CedarGroveStudios/PCB_Ibanez_FL-9_Flanger/media/2022-11-17_pcb_before.jpeg

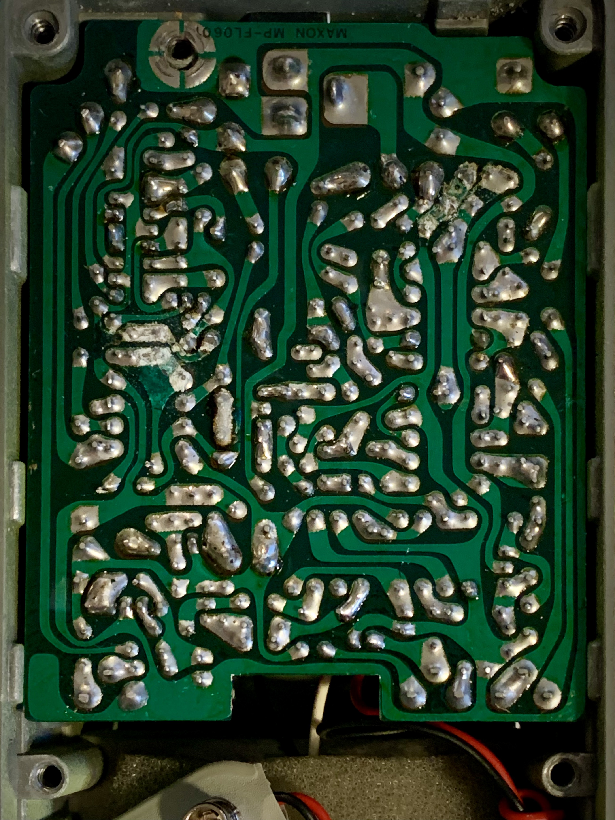
media/2022-11-17_pcb_before.jpeg
