CedarGroveStudios/PCB_Ibanez_FL-9_Flanger/media/cache_31260282.jpg

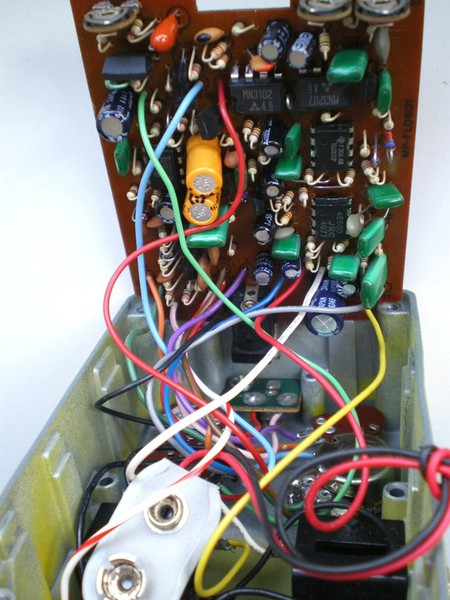
media/cache_31260282.jpg
