CedarGroveStudios/PCB_Ibanez_FL-9_Flanger/media/DigiKey_shipment_2022-11-08.jpeg

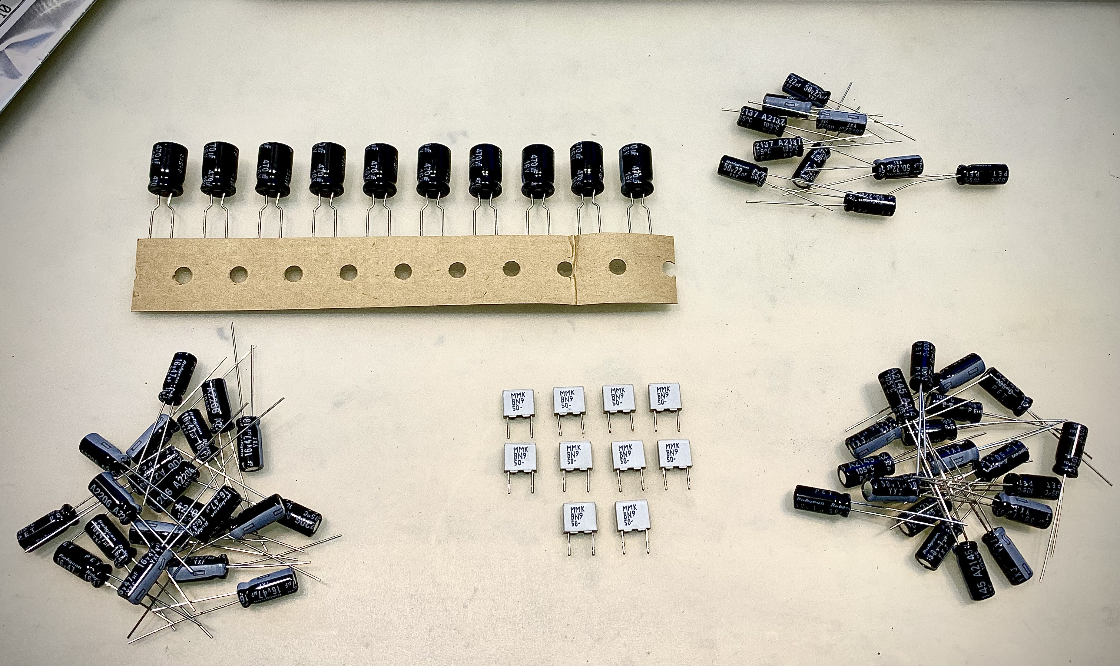
media/DigiKey_shipment_2022-11-08.jpeg
