CedarGroveStudios/PCB_Ibanez_FL-9_Flanger/media/FL9_cap-damaged-in-progress_2022-11-18.jpeg

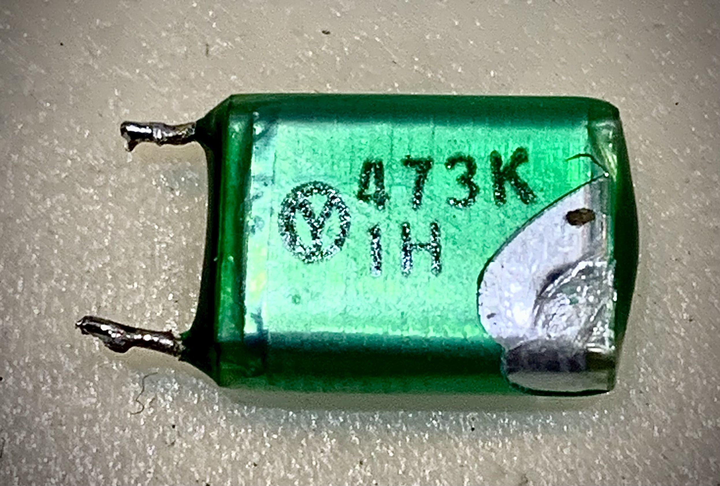
media/FL9_cap-damaged-in-progress_2022-11-18.jpeg
