CedarGroveStudios/PCB_Ibanez_FL-9_Flanger/media/FL9_PCB_before_close02_2022-11-17.jpeg

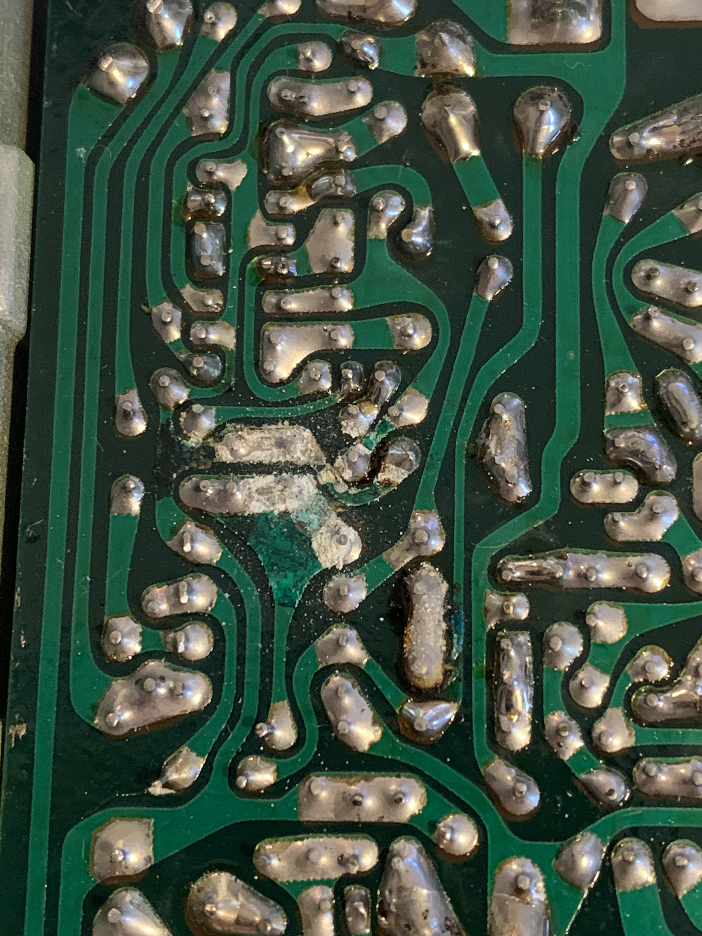
media/FL9_PCB_before_close02_2022-11-17.jpeg
