CedarGroveStudios/PCB_Ibanez_FL-9_Flanger/media/PCB_cleaned_before_close_02_2022-11-17.jpeg

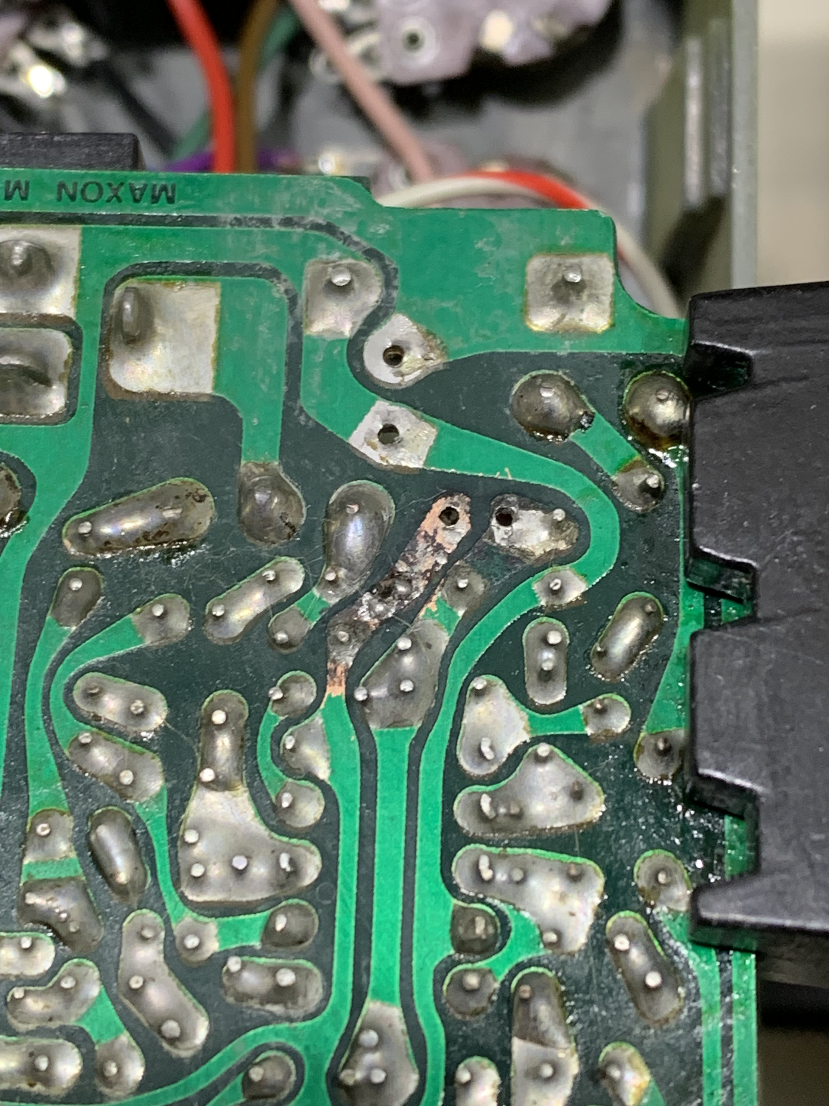
media/PCB_cleaned_before_close_02_2022-11-17.jpeg
