CedarGroveStudios/PCB_Ibanez_FL-9_Flanger/media/PCB_in-progress_close_03_2022-11-17.WEBP

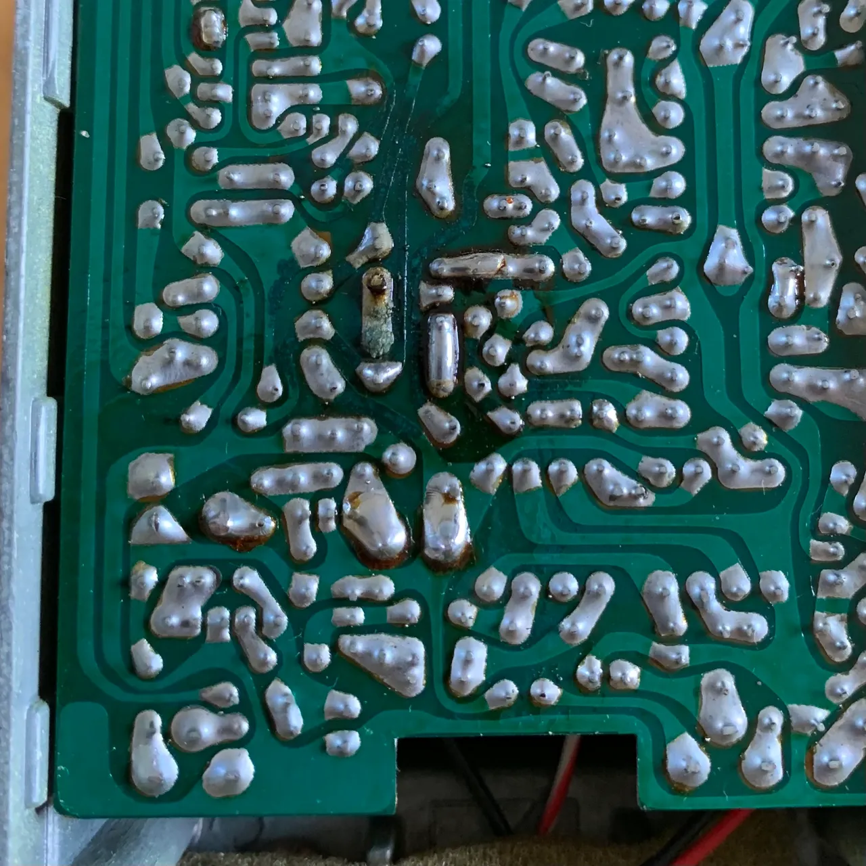
media/PCB_in-progress_close_03_2022-11-17.WEBP
