CedarGroveStudios/PCB_Ibanez_FL-9_Flanger/media/PCB_in-progress_close_04_2022-11-17.jpeg

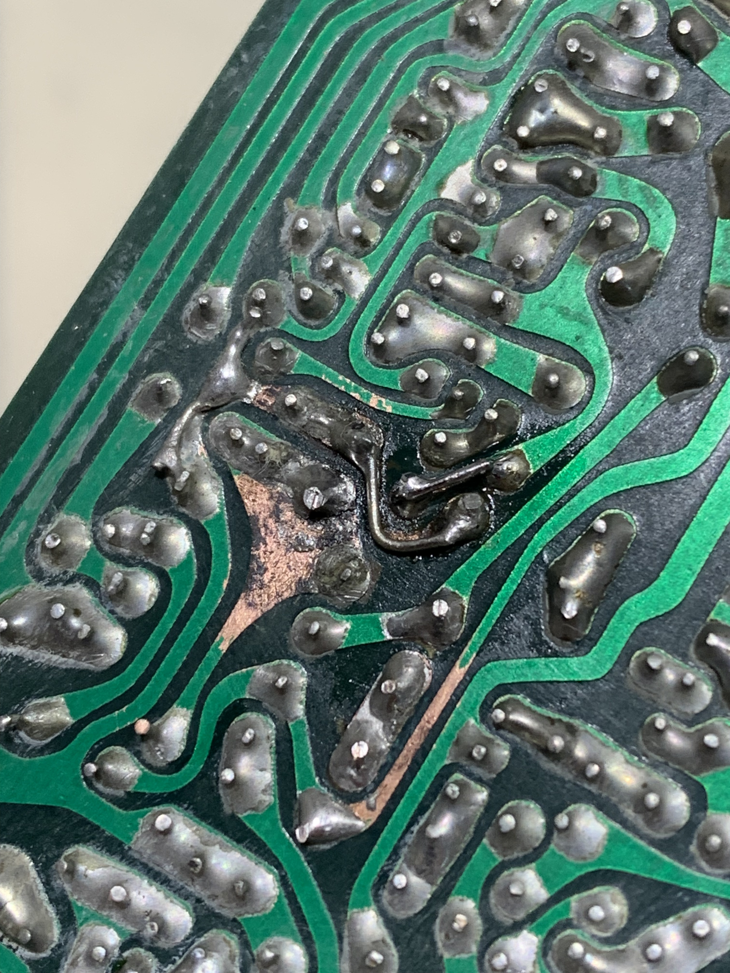
media/PCB_in-progress_close_04_2022-11-17.jpeg
