CedarGroveStudios/PCB_Ibanez_FL-9_Flanger/media/PCB_TOP_before_2022-11-17.jpeg

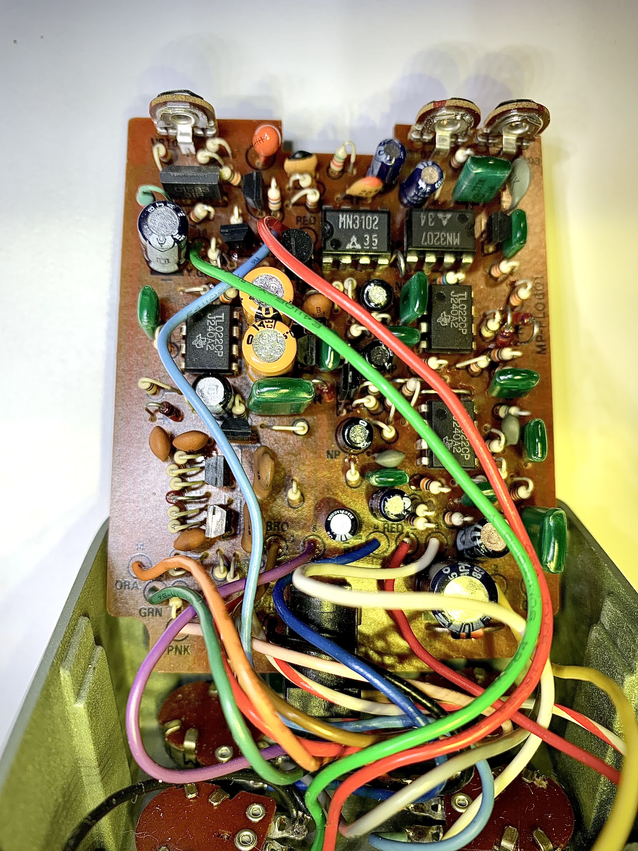
media/PCB_TOP_before_2022-11-17.jpeg
