CedarGroveStudios/PCB_Ibanez_FL-9_Flanger/PCB/FL9_PCB_BOT_traces_60x77mm.jpg

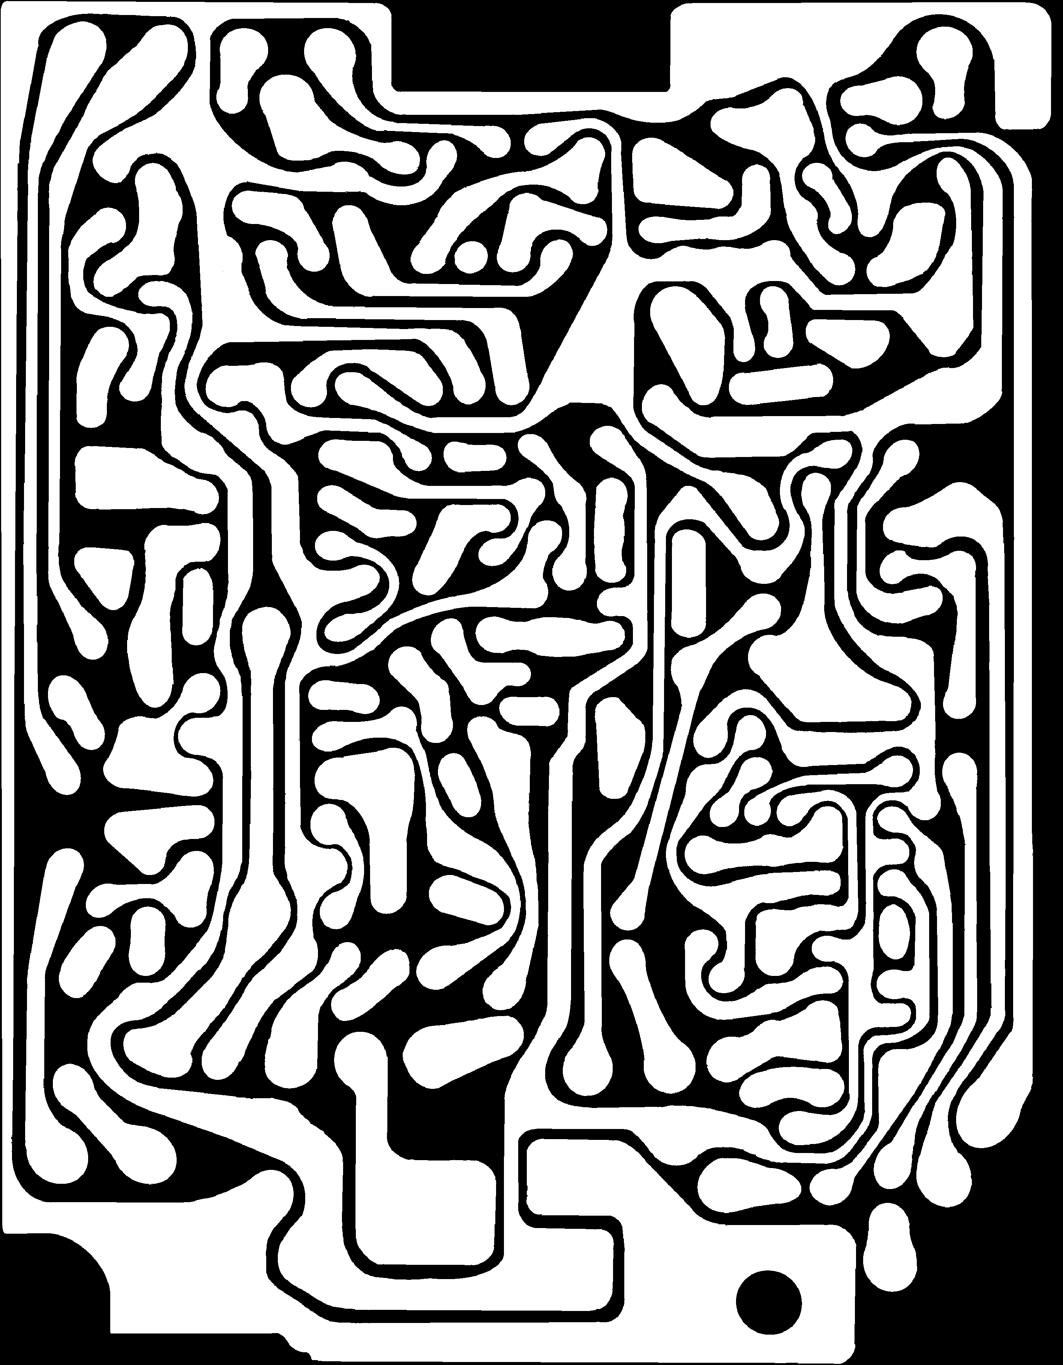
PCB/FL9_PCB_BOT_traces_60x77mm.jpg
