CedarGroveStudios/PCB_Ibanez_FL-9_Flanger/PCB/Ibanez_FL-9_bare_top.png

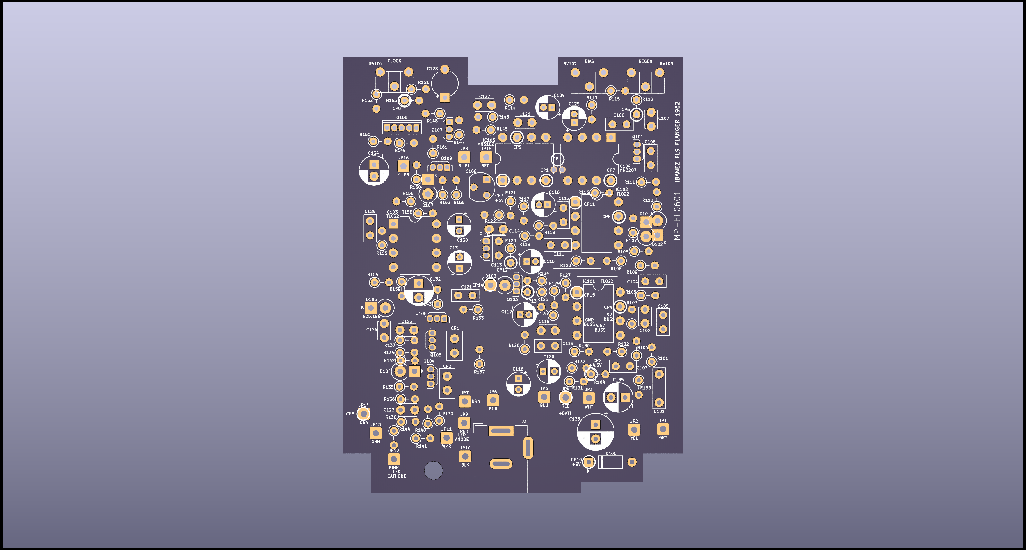
PCB/Ibanez_FL-9_bare_top.png
