CedarGroveStudios/PCB_Ibanez_FL-9_Flanger/reference/Electro-Harmonix_SMALL_STONE.jpg

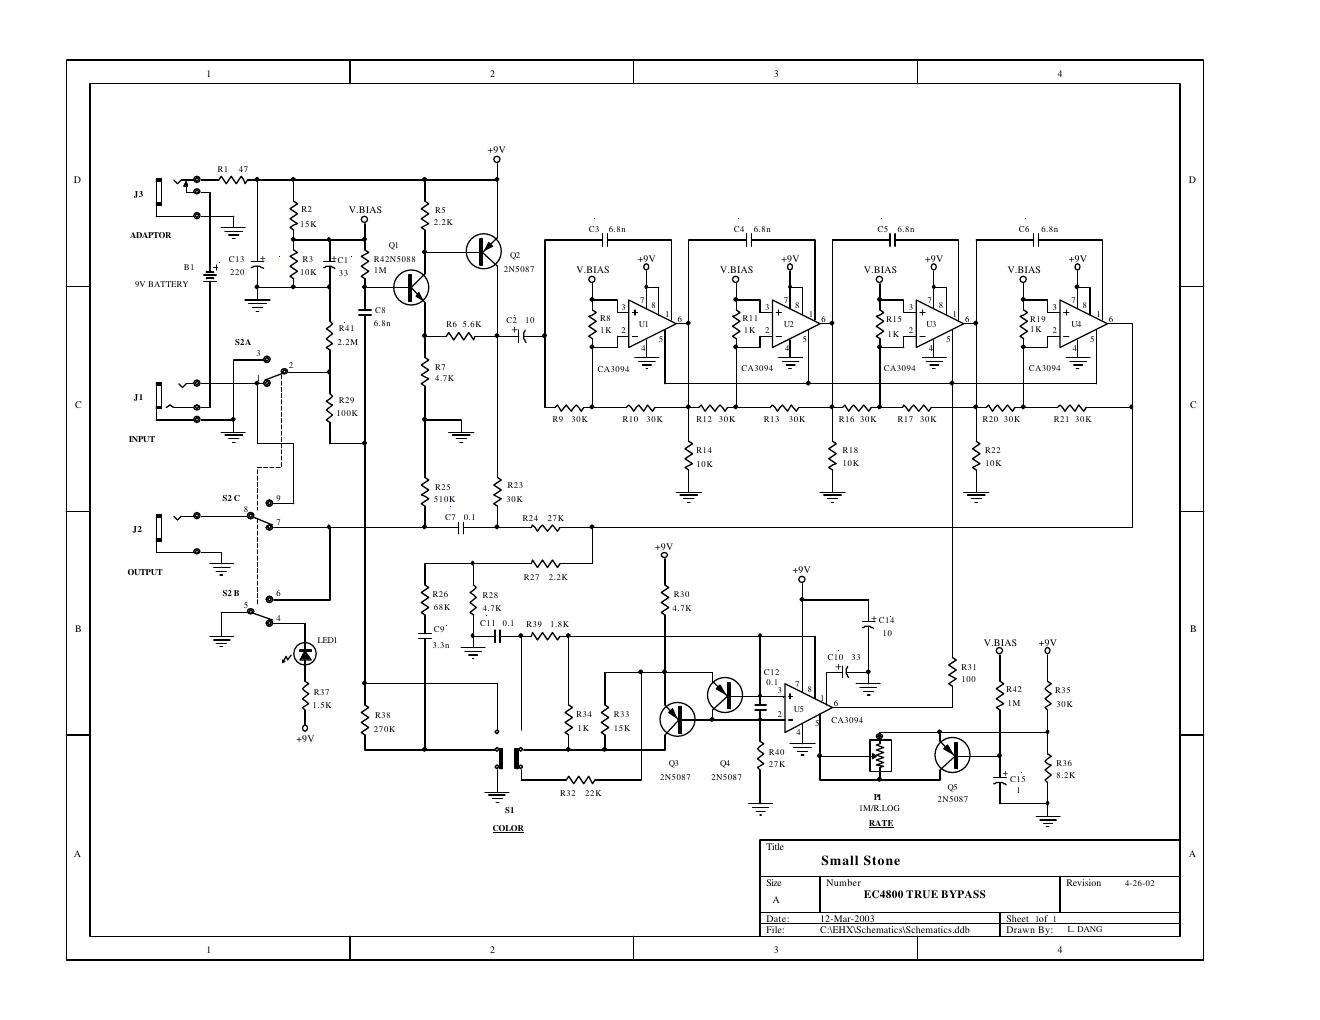
reference/Electro-Harmonix_SMALL_STONE.jpg
