CedarGroveStudios/PCB_Ibanez_FL-9_Flanger/media/guide_photos_and_graphics/bias_wave.png

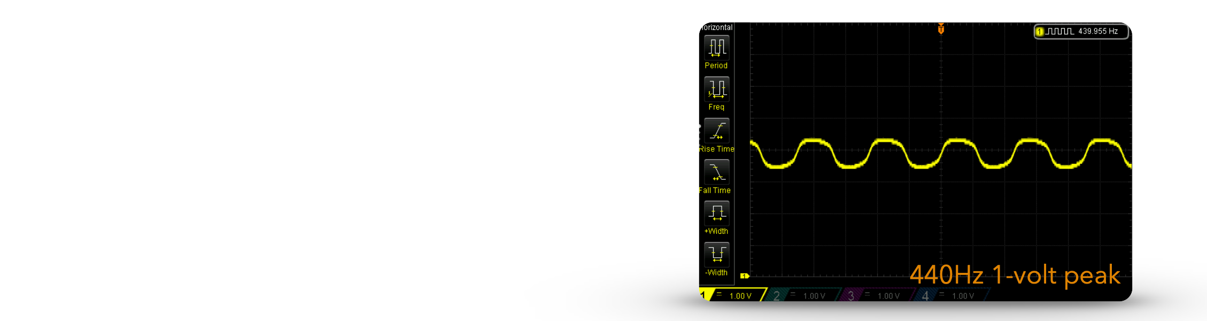
media/guide_photos_and_graphics/bias_wave.png
