CedarGroveStudios/PCB_Ibanez_FL-9_Flanger/media/guide_photos_and_graphics/block_diagram.png

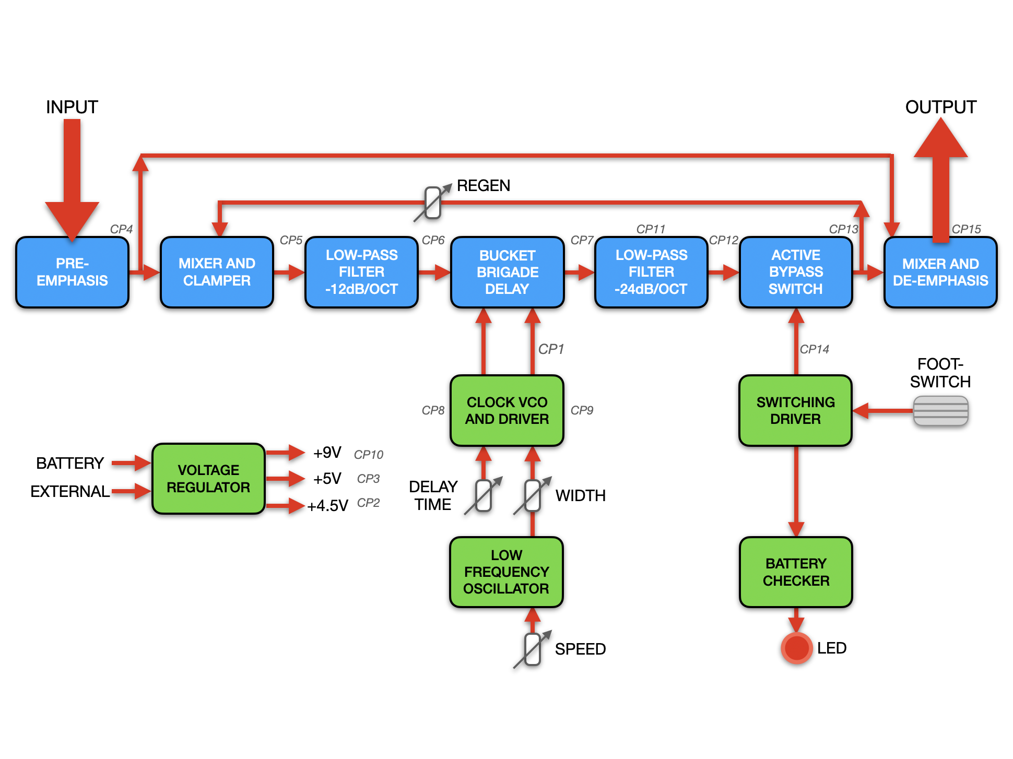
media/guide_photos_and_graphics/block_diagram.png
