CedarGroveStudios/PCB_Ibanez_FL-9_Flanger/media/guide_photos_and_graphics/clock_waves_composite.png

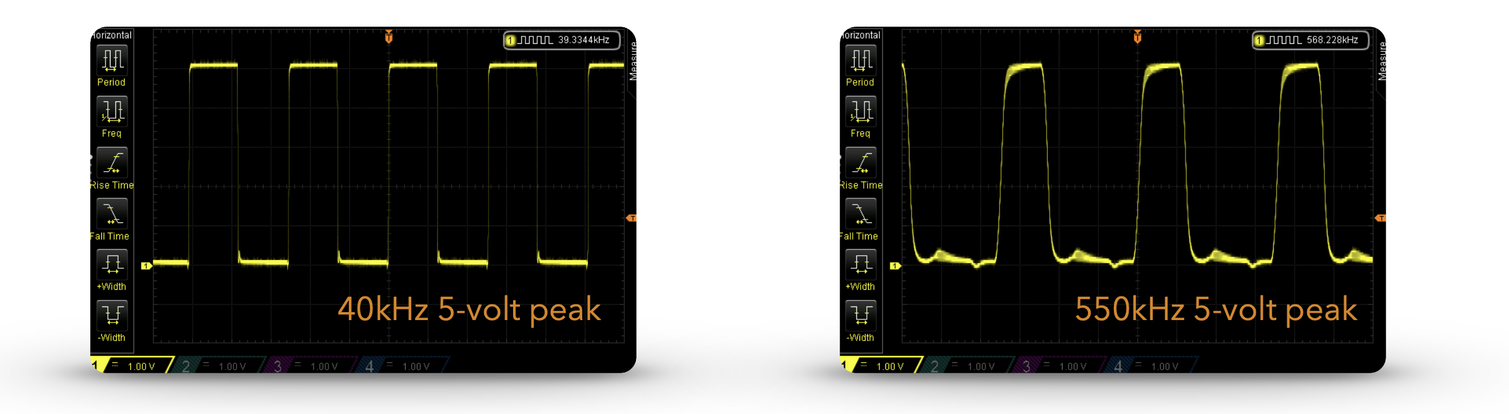
media/guide_photos_and_graphics/clock_waves_composite.png
