CedarGroveStudios/PCB_Ibanez_FL-9_Flanger/media/guide_photos_and_graphics/PCB_3D_render_glamour.png

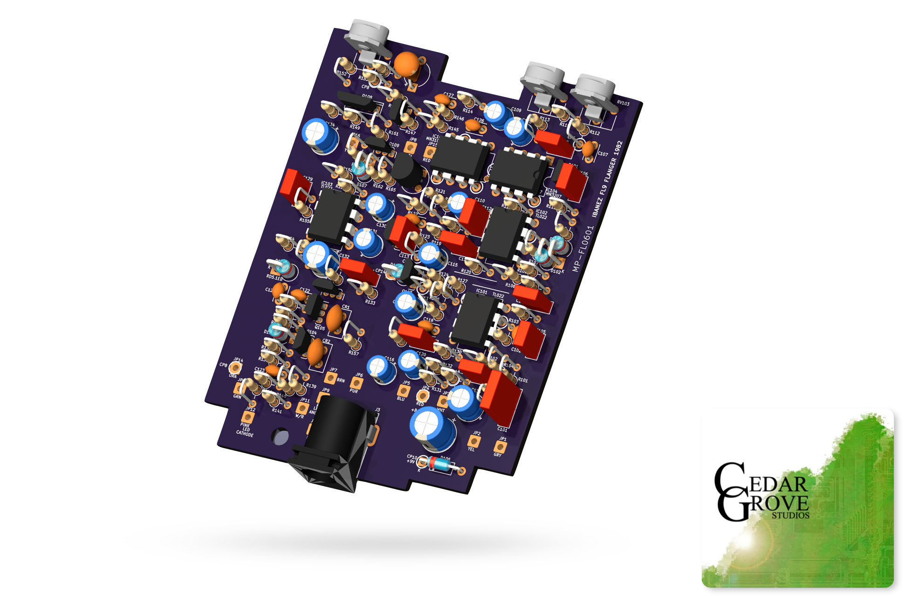
media/guide_photos_and_graphics/PCB_3D_render_glamour.png
