CedarGroveStudios/PCB_Ibanez_FL-9_Flanger/media/guide_photos_and_graphics/PCB_TOP_ortho_render.png

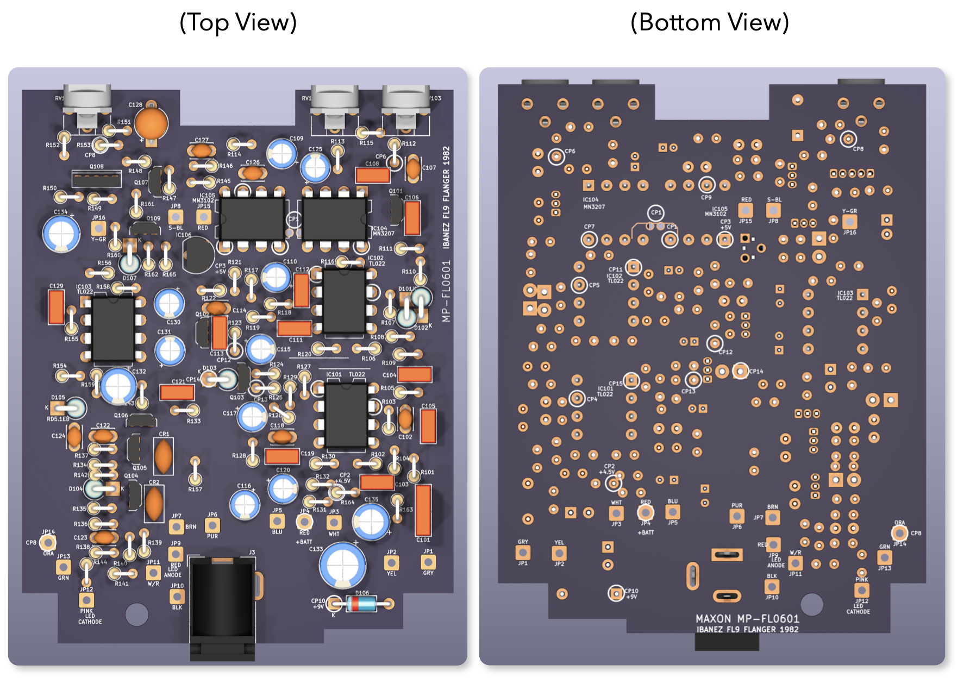
media/guide_photos_and_graphics/PCB_TOP_ortho_render.png
