CedarGroveStudios/PCB_Ibanez_FL-9_Flanger/media/guide_testpoint_waveforms/cp4_pre-emph_out.png

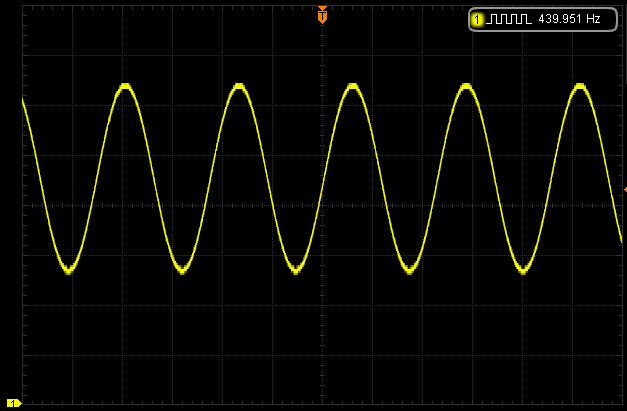
media/guide_testpoint_waveforms/cp4_pre-emph_out.png
