CedarGroveStudios/PCB_Ibanez_FL-9_Flanger/media/guide_testpoint_waveforms/cp5_mix_clamp_out.png

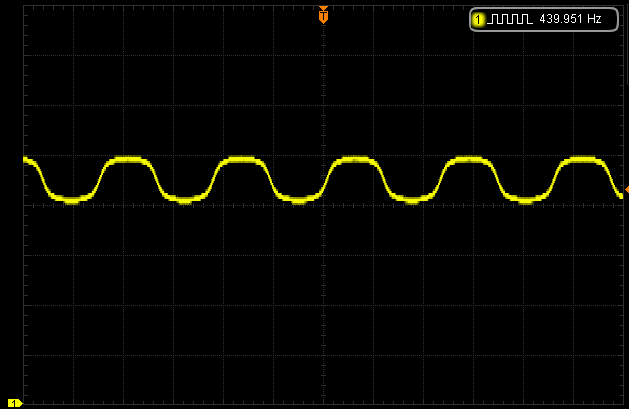
media/guide_testpoint_waveforms/cp5_mix_clamp_out.png
