CedarGroveStudios/PCB_Ibanez_FL-9_Flanger/media/guide_testpoint_waveforms/cp7_bbd_out.png

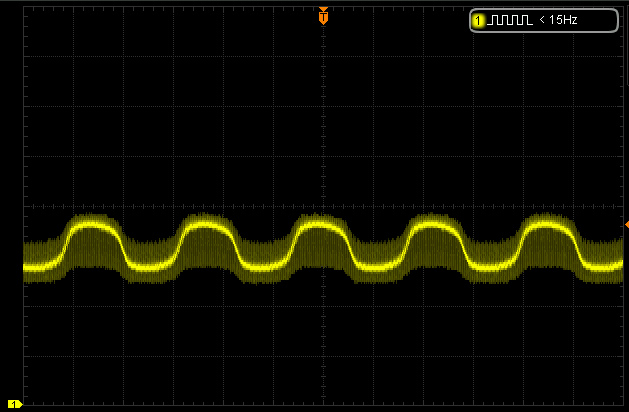
media/guide_testpoint_waveforms/cp7_bbd_out.png
