CedarGroveStudios/PCB_Ibanez_FL-9_Flanger/media/guide_testpoint_waveforms/cp9_clock_osc.png

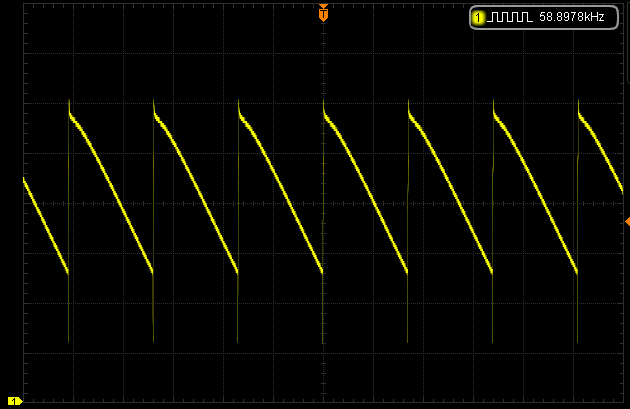
media/guide_testpoint_waveforms/cp9_clock_osc.png
