CedarGroveStudios/PCB_Ibanez_FL-9_Flanger/media/guide_testpoint_waveforms/cp12_low-pass_out.png

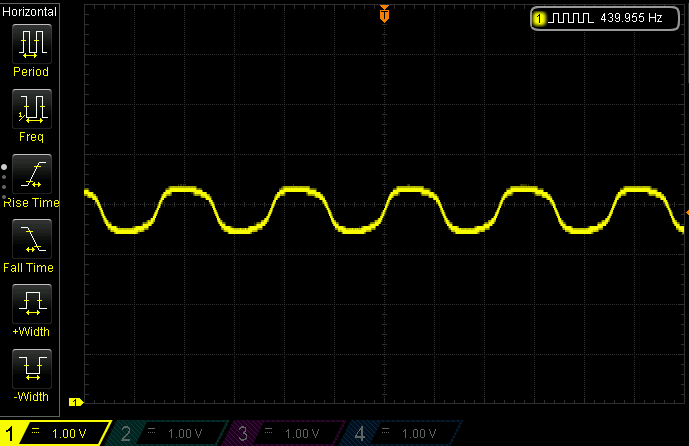
media/guide_testpoint_waveforms/cp12_low-pass_out.png
