CedarGroveStudios/PCB_Ibanez_FL-9_Flanger/media/working-on-guide_2022-11-25.jpeg

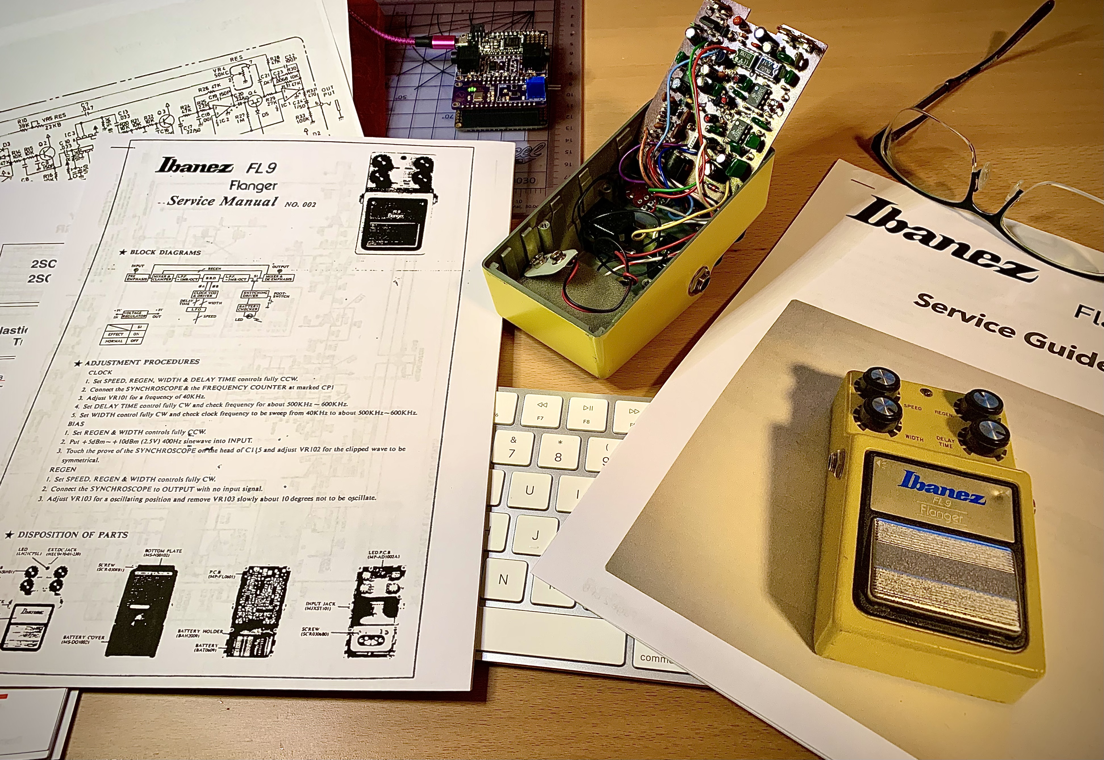
media/working-on-guide_2022-11-25.jpeg
