CedarGroveStudios/PCB_Ibanez_FL-9_Flanger/media/guide_photos_and_graphics/PCB_BOT_testpoints.png

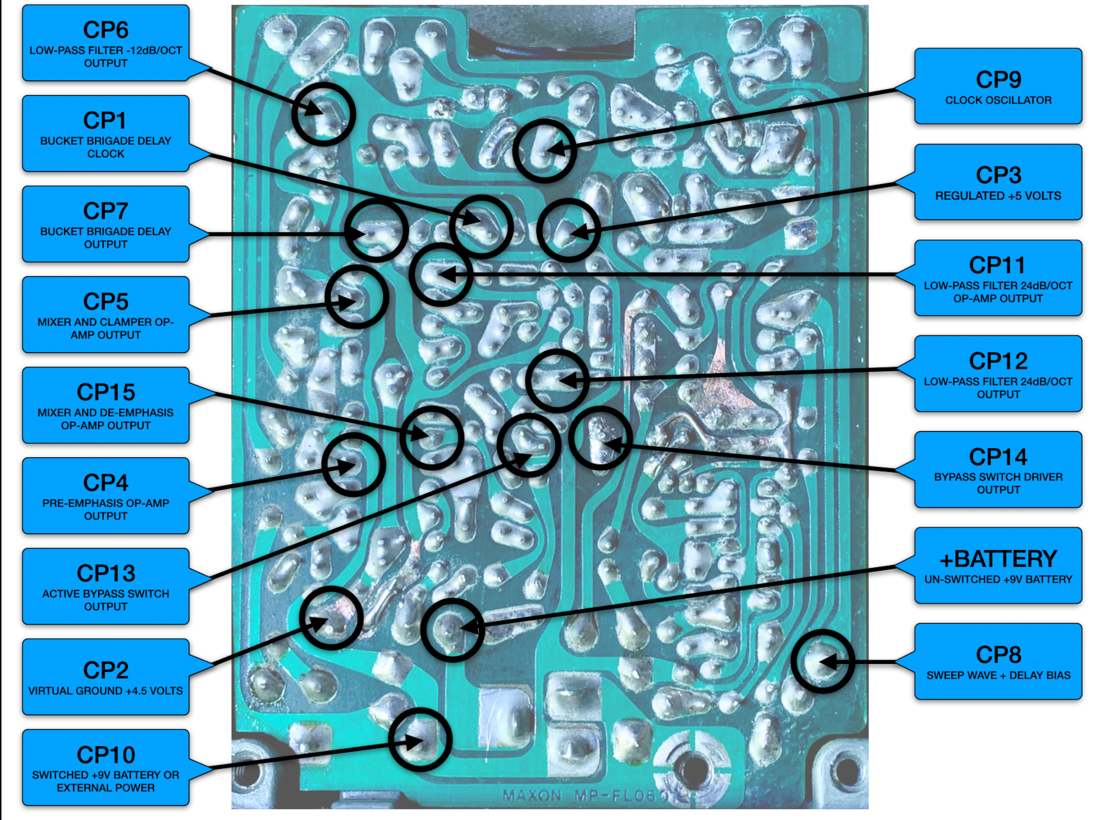
media/guide_photos_and_graphics/PCB_BOT_testpoints.png
