CedarGroveStudios/PCB_Ibanez_FL-9_Flanger/media/guide_testpoint_waveforms/cp1_test_clock_40kHz.png

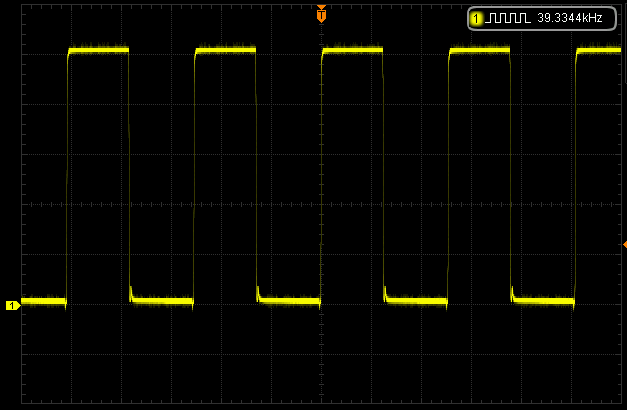
media/guide_testpoint_waveforms/cp1_test_clock_40kHz.png
