CedarGroveStudios/PCB_Ibanez_FL-9_Flanger/media/guide_testpoint_waveforms/cp8_test_sweep.png

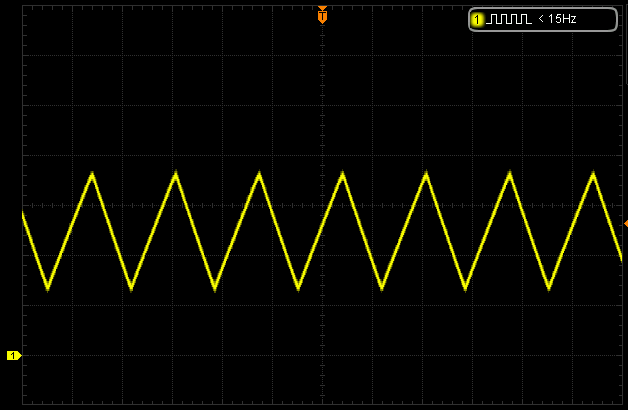
media/guide_testpoint_waveforms/cp8_test_sweep.png
