CedarGroveStudios/PCB_Ibanez_FL-9_Flanger/media/testpoint-overlay_2022-12-04.jpeg

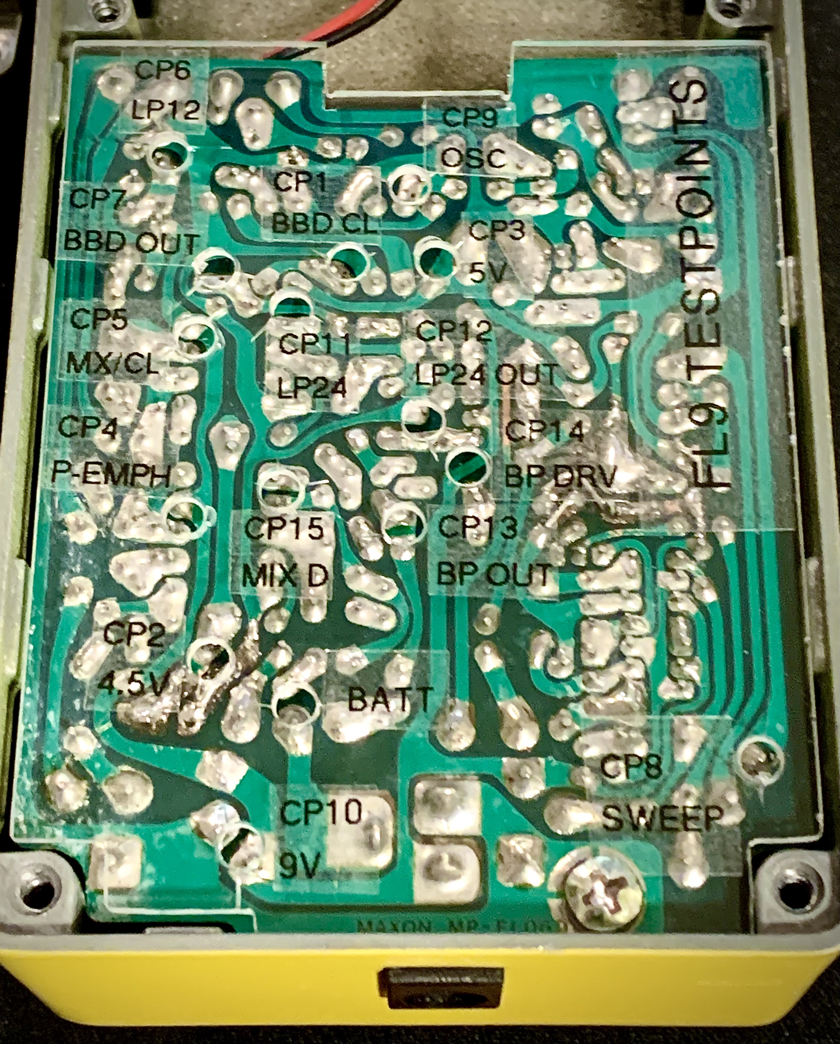
media/testpoint-overlay_2022-12-04.jpeg
