CedarGroveStudios/PCB_Ibanez_FL-9_Flanger/media/guide_photos_and_graphics/troubleshooting_01.png

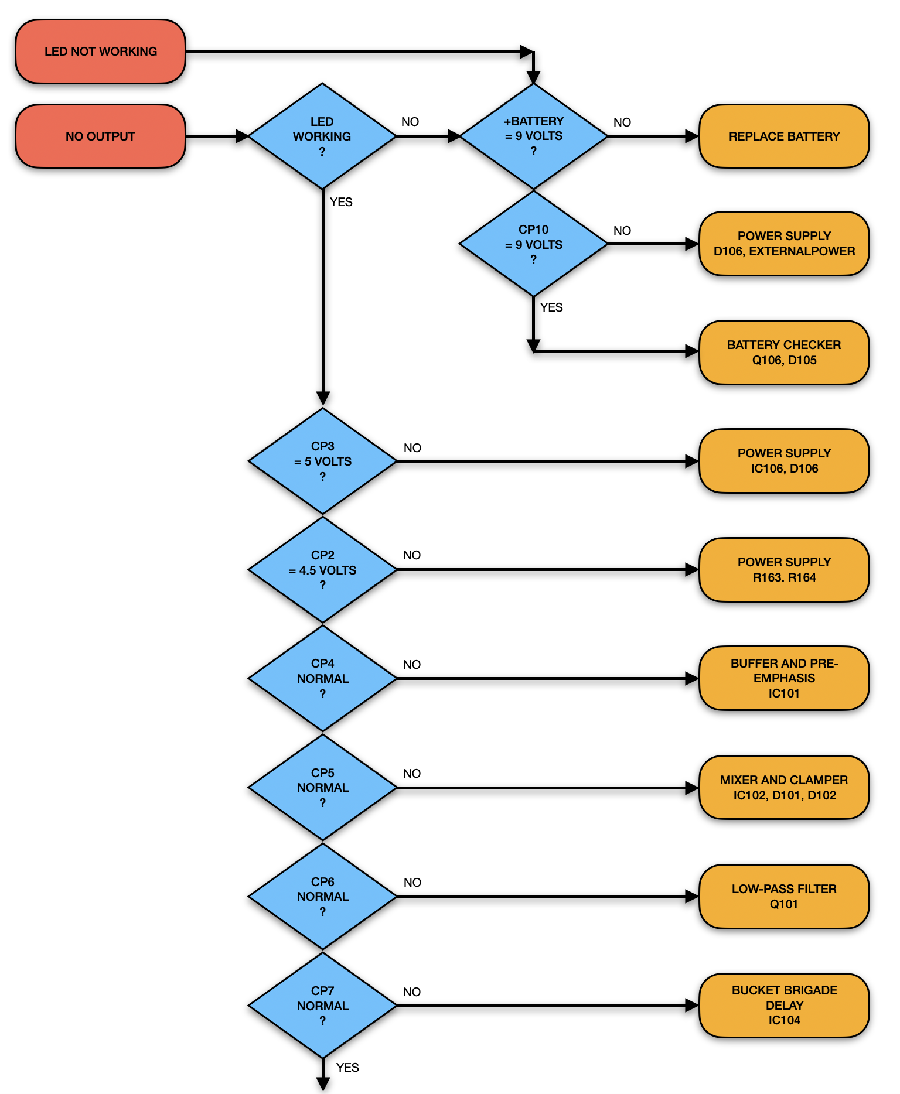
media/guide_photos_and_graphics/troubleshooting_01.png
